TNTBA/OrangeStorm-Giga-Profile-for-Orca/orca_slicer_config/profiles/Elegoo/Elegoo Neptune 2S_cover.png

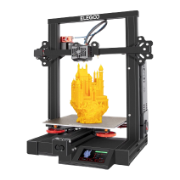
orca_slicer_config/profiles/Elegoo/Elegoo Neptune 2S_cover.png
