TNTBA/OrangeStorm-Giga-Profile-for-Orca/orca_slicer_config/profiles/Elegoo/Elegoo Orangestorm Giga_cover.png

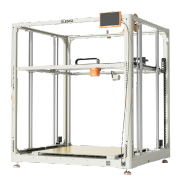
orca_slicer_config/profiles/Elegoo/Elegoo Orangestorm Giga_cover.png
