TNTBA/OrangeStorm-Giga-Profile-for-Orca/orca_slicer_config/profiles/Elegoo/elegoo_neptune2_buildplate_texture.png

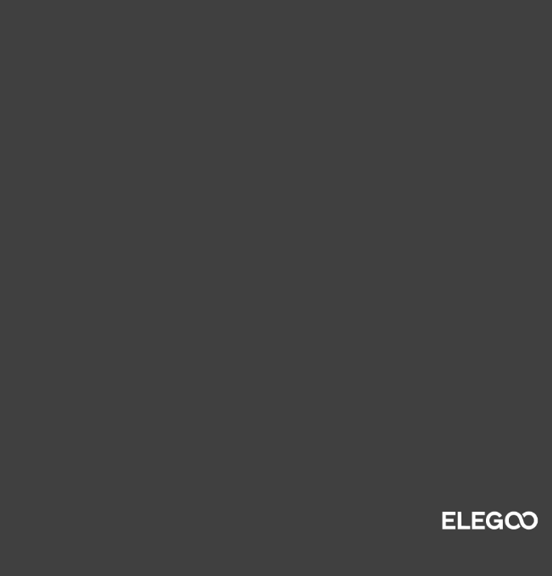
orca_slicer_config/profiles/Elegoo/elegoo_neptune2_buildplate_texture.png
